sandman72/aZ80_Computer/Software/VDP_Firmware/aZ80_VDP/keyboard.ino

//--------------------------------------------------------------------+
// Keyboard Layouts  (three parameters -> lowercase, shifted, altgr )
//--------------------------------------------------------------------+
#define SCANCODE_F1  0x3a
#define SCANCODE_F2  0x3b
#define SCANCODE_F3  0x3c
#define SCANCODE_F4  0x3d
#define SCANCODE_F5  0x3e
#define SCANCODE_F6  0x3f
#define SCANCODE_F7  0x40
#define SCANCODE_F8  0x41
#define SCANCODE_F9  0x42
#define SCANCODE_F10 0x43
#define SCANCODE_F11 0x44
#define SCANCODE_F12 0x45

#define SCANCODE_HOME   0x4a
#define SCANCODE_PGUP   0x4b
#define SCANCODE_PGDOWN 0x4e
#define SCANCODE_RIGHT  0x4f
#define SCANCODE_LEFT   0x50
#define SCANCODE_DOWN   0x51
#define SCANCODE_UP     0x52

#define HID_KEYCODE_TO_ASCII_US     \
    {0     , 0     ,0 }, /* 0x00 */ \
    {0     , 0     ,0 }, /* 0x01 */ \
    {0     , 0     ,0 }, /* 0x02 */ \
    {0     , 0     ,0 }, /* 0x03 */ \
    {'a'   , 'A'   ,0 }, /* 0x04 */ \
    {'b'   , 'B'   ,0 }, /* 0x05 */ \
    {'c'   , 'C'   ,0 }, /* 0x06 */ \
    {'d'   , 'D'   ,0 }, /* 0x07 */ \
    {'e'   , 'E'   ,0 }, /* 0x08 */ \
    {'f'   , 'F'   ,0 }, /* 0x09 */ \
    {'g'   , 'G'   ,0 }, /* 0x0a */ \
    {'h'   , 'H'   ,0 }, /* 0x0b */ \
    {'i'   , 'I'   ,0 }, /* 0x0c */ \
    {'j'   , 'J'   ,0 }, /* 0x0d */ \
    {'k'   , 'K'   ,0 }, /* 0x0e */ \
    {'l'   , 'L'   ,0 }, /* 0x0f */ \
    {'m'   , 'M'   ,0 }, /* 0x10 */ \
    {'n'   , 'N'   ,0 }, /* 0x11 */ \
    {'o'   , 'O'   ,0 }, /* 0x12 */ \
    {'p'   , 'P'   ,0 }, /* 0x13 */ \
    {'q'   , 'Q'   ,0 }, /* 0x14 */ \
    {'r'   , 'R'   ,0 }, /* 0x15 */ \
    {'s'   , 'S'   ,0 }, /* 0x16 */ \
    {'t'   , 'T'   ,0 }, /* 0x17 */ \
    {'u'   , 'U'   ,0 }, /* 0x18 */ \
    {'v'   , 'V'   ,0 }, /* 0x19 */ \
    {'w'   , 'W'   ,0 }, /* 0x1a */ \
    {'x'   , 'X'   ,0 }, /* 0x1b */ \
    {'y'   , 'Y'   ,0 }, /* 0x1c */ \
    {'z'   , 'Z'   ,0 }, /* 0x1d */ \
    {'1'   , '!'   ,0 }, /* 0x1e */ \
    {'2'   , '@'   ,0 }, /* 0x1f */ \
    {'3'   , '#'   ,0 }, /* 0x20 */ \
    {'4'   , '$'   ,0 }, /* 0x21 */ \
    {'5'   , '%'   ,0 }, /* 0x22 */ \
    {'6'   , '^'   ,0 }, /* 0x23 */ \
    {'7'   , '&'   ,0 }, /* 0x24 */ \
    {'8'   , '*'   ,0 }, /* 0x25 */ \
    {'9'   , '('   ,0 }, /* 0x26 */ \
    {'0'   , ')'   ,0 }, /* 0x27 */ \
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
    {0     , 0     ,0 }, /* 0x49 INS   */ \
    {0     , 0     ,0 }, /* 0x4a       */ \
    {0     , 0     ,0 }, /* 0x4b PGUP  */ \
    {0x7f  , 0     ,0 }, /* 0x4c DEL   */ \
    {0     , 0     ,0 }, /* 0x4d       */ \
    {0     , 0     ,0 }, /* 0x4e PGDN  */ \
    {0     , 0     ,0 }, /* 0x4f RIGHT */ \
    {0     , 0     ,0 }, /* 0x50 LEFT  */ \
    {0     , 0     ,0 }, /* 0x51 DOWN  */ \
    {0     , 0     ,0 }, /* 0x52 UP    */ \
    {0     , 0     ,0 }, /* 0x53       */ \
    {'/'   , '/'   ,0 }, /* 0x54 */ \
    {'*'   , '*'   ,0 }, /* 0x55 */ \
    {'-'   , '-'   ,0 }, /* 0x56 */ \
    {'+'   , '+'   ,0 }, /* 0x57 */ \
    {'\r'  , '\r'  ,0 }, /* 0x58 */ \
    {'1'   , 0     ,0 }, /* 0x59 */ \
    {'2'   , 0     ,0 }, /* 0x5a */ \
    {'3'   , 0     ,0 }, /* 0x5b */ \
    {'4'   , 0     ,0 }, /* 0x5c */ \
    {'5'   , '5'   ,0 }, /* 0x5d */ \
    {'6'   , 0     ,0 }, /* 0x5e */ \
    {'7'   , 0     ,0 }, /* 0x5f */ \
    {'8'   , 0     ,0 }, /* 0x60 */ \
    {'9'   , 0     ,0 }, /* 0x61 */ \
    {'0'   , 0     ,0 }, /* 0x62 */ \
    {'0'   , 0     ,0 }, /* 0x63 */ \
    {'='   , '='   ,0 }, /* 0x67 */ \

#define HID_KEYCODE_TO_ASCII_UK     \
    {0     , 0     ,0 }, /* 0x00 */ \
    {0     , 0     ,0 }, /* 0x01 */ \
    {0     , 0     ,0 }, /* 0x02 */ \
    {0     , 0     ,0 }, /* 0x03 */ \
    {'a'   , 'A'   ,0 }, /* 0x04 */ \
    {'b'   , 'B'   ,0 }, /* 0x05 */ \
    {'c'   , 'C'   ,0 }, /* 0x06 */ \
    {'d'   , 'D'   ,0 }, /* 0x07 */ \
    {'e'   , 'E'   ,0 }, /* 0x08 */ \
    {'f'   , 'F'   ,0 }, /* 0x09 */ \
    {'g'   , 'G'   ,0 }, /* 0x0a */ \
    {'h'   , 'H'   ,0 }, /* 0x0b */ \
    {'i'   , 'I'   ,0 }, /* 0x0c */ \
    {'j'   , 'J'   ,0 }, /* 0x0d */ \
    {'k'   , 'K'   ,0 }, /* 0x0e */ \
    {'l'   , 'L'   ,0 }, /* 0x0f */ \
    {'m'   , 'M'   ,0 }, /* 0x10 */ \
    {'n'   , 'N'   ,0 }, /* 0x11 */ \
    {'o'   , 'O'   ,0 }, /* 0x12 */ \
    {'p'   , 'P'   ,0 }, /* 0x13 */ \
    {'q'   , 'Q'   ,0 }, /* 0x14 */ \
    {'r'   , 'R'   ,0 }, /* 0x15 */ \
    {'s'   , 'S'   ,0 }, /* 0x16 */ \
    {'t'   , 'T'   ,0 }, /* 0x17 */ \
    {'u'   , 'U'   ,0 }, /* 0x18 */ \
    {'v'   , 'V'   ,0 }, /* 0x19 */ \
    {'w'   , 'W'   ,0 }, /* 0x1a */ \
    {'x'   , 'X'   ,0 }, /* 0x1b */ \
    {'y'   , 'Y'   ,0 }, /* 0x1c */ \
    {'z'   , 'Z'   ,0 }, /* 0x1d */ \
    {'1'   , '!'   ,0 }, /* 0x1e */ \
    {'2'   , '\"'  ,0 }, /* 0x1f */ \
    {'3'   , '#'   ,0 }, /* 0x20 */ \
    {'4'   , '$'   ,0 }, /* 0x21 */ \
    {'5'   , '%'   ,0 }, /* 0x22 */ \
    {'6'   , '^'   ,0 }, /* 0x23 */ \
    {'7'   , '&'   ,0 }, /* 0x24 */ \
    {'8'   , '*'   ,0 }, /* 0x25 */ \
    {'9'   , '('   ,0 }, /* 0x26 */ \
    {'0'   , ')'   ,0 }, /* 0x27 */ \
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
    {0     , 0     ,0 }, /* 0x49 INS   */ \
    {0     , 0     ,0 }, /* 0x4a       */ \
    {0     , 0     ,0 }, /* 0x4b PGUP  */ \
    {0     , 0     ,0 }, /* 0x4c DEL   */ \
    {0     , 0     ,0 }, /* 0x4d       */ \
    {0     , 0     ,0 }, /* 0x4e PGDN  */ \
    {0     , 0     ,0 }, /* 0x4f RIGHT */ \
    {0     , 0     ,0 }, /* 0x50 LEFT  */ \
    {0     , 0     ,0 }, /* 0x51 DOWN  */ \
    {0     , 0     ,0 }, /* 0x52 UP    */ \
    {0     , 0     ,0 }, /* 0x53       */ \
    {'/'   , '/'   ,0 }, /* 0x54 */ \
    {'*'   , '*'   ,0 }, /* 0x55 */ \
    {'-'   , '-'   ,0 }, /* 0x56 */ \
    {'+'   , '+'   ,0 }, /* 0x57 */ \
    {'\r'  , '\r'  ,0 }, /* 0x58 */ \
    {'1'   , 0     ,0 }, /* 0x59 */ \
    {'2'   , 0     ,0 }, /* 0x5a */ \
    {'3'   , 0     ,0 }, /* 0x5b */ \
    {'4'   , 0     ,0 }, /* 0x5c */ \
    {'5'   , '5'   ,0 }, /* 0x5d */ \
    {'6'   , 0     ,0 }, /* 0x5e */ \
    {'7'   , 0     ,0 }, /* 0x5f */ \
    {'8'   , 0     ,0 }, /* 0x60 */ \
    {'9'   , 0     ,0 }, /* 0x61 */ \
    {'0'   , 0     ,0 }, /* 0x62 */ \
    {'0'   , 0     ,0 }, /* 0x63 */ \
    {'\\'  , '|'   ,0 }, /* 0x64 */ \
    {'0'   , 0     ,0 }, /* 0x65 */ \
    {'0'   , 0     ,0 }, /* 0x66 */ \
    {'='   , '='   ,0 }, /* 0x67 */ \

#define HID_KEYCODE_TO_ASCII_DE      \
     {0     , 0     ,0 }, /* 0x00 */ \
     {0     , 0     ,0 }, /* 0x01 */ \
     {0     , 0     ,0 }, /* 0x02 */ \
     {0     , 0     ,0 }, /* 0x03 */ \
     {'a'   , 'A'   ,0 }, /* 0x04 */ \
     {'b'   , 'B'   ,0 }, /* 0x05 */ \
     {'c'   , 'C'   ,0 }, /* 0x06 */ \
     {'d'   , 'D'   ,0 }, /* 0x07 */ \
     {'e'   , 'E'   ,0 }, /* 0x08 */ \
     {'f'   , 'F'   ,0 }, /* 0x09 */ \
     {'g'   , 'G'   ,0 }, /* 0x0a */ \
     {'h'   , 'H'   ,0 }, /* 0x0b */ \
     {'i'   , 'I'   ,0 }, /* 0x0c */ \
     {'j'   , 'J'   ,0 }, /* 0x0d */ \
     {'k'   , 'K'   ,0 }, /* 0x0e */ \
     {'l'   , 'L'   ,0 }, /* 0x0f */ \
     {'m'   , 'M'   ,0 }, /* 0x10 */ \
     {'n'   , 'N'   ,0 }, /* 0x11 */ \
     {'o'   , 'O'   ,0 }, /* 0x12 */ \
     {'p'   , 'P'   ,0 }, /* 0x13 */ \
     {'q'   , 'Q' , '@'}, /* 0x14 */ \
     {'r'   , 'R'   ,0 }, /* 0x15 */ \
     {'s'   , 'S'   ,0 }, /* 0x16 */ \
     {'t'   , 'T'   ,0 }, /* 0x17 */ \
     {'u'   , 'U'   ,0 }, /* 0x18 */ \
     {'v'   , 'V'   ,0 }, /* 0x19 */ \
     {'w'   , 'W'   ,0 }, /* 0x1a */ \
     {'x'   , 'X'   ,0 }, /* 0x1b */ \
     {'z'   , 'Z'   ,0 }, /* 0x1c */ \
     {'y'   , 'Y'   ,0 }, /* 0x1d */ \
     {'1'   , '!'   ,0 }, /* 0x1e */ \
     {'2'   , '\"'  ,0 }, /* 0x1f */ \
     {'3'   , 0     ,0 }, /* 0x20 */ \
     {'4'   , '$'   ,0 }, /* 0x21 */ \
     {'5'   , '%'   ,0 }, /* 0x22 */ \
     {'6'   , '&'   ,0 }, /* 0x23 */ \
     {'7'   , '/' ,'{' }, /* 0x24 */ \
     {'8'   , '(' ,'[' }, /* 0x25 */ \
     {'9'   , ')' ,']' }, /* 0x26 */ \
     {'0'   , '=' ,'}' }, /* 0x27 */ \
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
     {0     , 0     ,0 }, /* 0x49 INS   */ \
     {0     , 0     ,0 }, /* 0x4a       */ \
     {0     , 0     ,0 }, /* 0x4b PGUP  */ \
     {0x7f  , 0     ,0 }, /* 0x4c DEL   */ \
     {0     , 0     ,0 }, /* 0x4d       */ \
     {0     , 0     ,0 }, /* 0x4e PGDN  */ \
     {0     , 0     ,0 }, /* 0x4f RIGHT */ \
     {0     , 0     ,0 }, /* 0x50 LEFT  */ \
     {0     , 0     ,0 }, /* 0x51 DOWN  */ \
     {0     , 0     ,0 }, /* 0x52 UP    */ \
     {0     , 0     ,0 }, /* 0x53       */ \
     {'/'   , '/'   ,0 }, /* 0x54 */ \
     {'*'   , '*'   ,0 }, /* 0x55 */ \
     {'-'   , '-'   ,0 }, /* 0x56 */ \
     {'+'   , '+'   ,0 }, /* 0x57 */ \
     {'\r'  , '\r'  ,0 }, /* 0x58 */ \
     {'1'   , 0     ,0 }, /* 0x59 */ \
     {'2'   , 0     ,0 }, /* 0x5a */ \
     {'3'   , 0     ,0 }, /* 0x5b */ \
     {'4'   , 0     ,0 }, /* 0x5c */ \
     {'5'   , '5'   ,0 }, /* 0x5d */ \
     {'6'   , 0     ,0 }, /* 0x5e */ \
     {'7'   , 0     ,0 }, /* 0x5f */ \
     {'8'   , 0     ,0 }, /* 0x60 */ \
     {'9'   , 0     ,0 }, /* 0x61 */ \
     {'0'   , 0     ,0 }, /* 0x62 */ \
     {'.'   , 0     ,0 }, /* 0x63 */ \
     {'<' , '>'   ,'|' }, /* 0x64 */ \
     {'0'   , 0     ,0 }, /* 0x65 */ \
     {'0'   , 0     ,0 }, /* 0x66 */ \
     {'='   , '='   ,0 }, /* 0x67 */ \

#define HID_KEYCODE_TO_ASCII_FR      \
     {0     , 0     ,0 }, /* 0x00 */ \
     {0     , 0     ,0 }, /* 0x01 */ \
     {0     , 0     ,0 }, /* 0x02 */ \
     {0     , 0     ,0 }, /* 0x03 */ \
     {'q'   , 'Q'   ,0 }, /* 0x04 */ \
     {'b'   , 'B'   ,0 }, /* 0x05 */ \
     {'c'   , 'C'   ,0 }, /* 0x06 */ \
     {'d'   , 'D'   ,0 }, /* 0x07 */ \
     {'e'   , 'E'   ,0 }, /* 0x08 (alt=EUR)*/ \
     {'f'   , 'F'   ,0 }, /* 0x09 */ \
     {'g'   , 'G'   ,0 }, /* 0x0a */ \
     {'h'   , 'H'   ,0 }, /* 0x0b */ \
     {'i'   , 'I'   ,0 }, /* 0x0c */ \
     {'j'   , 'J'   ,0 }, /* 0x0d */ \
     {'k'   , 'K'   ,0 }, /* 0x0e */ \
     {'l'   , 'L'   ,0 }, /* 0x0f */ \
     {','   , '?'   ,0 }, /* 0x10 */ \
     {'n'   , 'N'   ,0 }, /* 0x11 */ \
     {'o'   , 'O'   ,0 }, /* 0x12 */ \
     {'p'   , 'P'   ,0 }, /* 0x13 */ \
     {'a'   , 'A'  ,'@'}, /* 0x14 */ \
     {'r'   , 'R'   ,0 }, /* 0x15 */ \
     {'s'   , 'S'   ,0 }, /* 0x16 */ \
     {'t'   , 'T'   ,0 }, /* 0x17 */ \
     {'u'   , 'U'   ,0 }, /* 0x18 */ \
     {'v'   , 'V'   ,0 }, /* 0x19 */ \
     {'z'   , 'Z'   ,0 }, /* 0x1a */ \
     {'x'   , 'X'   ,0 }, /* 0x1b */ \
     {'y'   , 'Y'   ,0 }, /* 0x1c */ \
     {'w'   , 'W'   ,0 }, /* 0x1d */ \
     {'&'   , '1'   ,0 }, /* 0x1e */ \
     {'e'   , '2'  ,'~'}, /* 0x1f =é */ \
     {'\"'  , '3'  ,'#'}, /* 0x20 */ \
     {'\''  , '4'  ,'{'}, /* 0x21 */ \
     {'('   , '5'  ,'['}, /* 0x22 */ \
     {'-'   , '6'  ,'|'}, /* 0x23 */ \
     {'e'   , '7'  ,'`'}, /* 0x24 =è */ \
     {'_'   , '8' ,'\\'}, /* 0x25 */ \
     {'c'   , '9'  ,'^'}, /* 0x26 =ç */ \
     {'a'   , '0'  ,'@'}, /* 0x27 =à */ \
     {'\r'  , '\r'  ,0 }, /* 0x28 */ \
     {'\x1b', '\x1b',0 }, /* 0x29 */ \
     {'\b'  , '\b'  ,0 }, /* 0x2a */ \
     {'\t'  , '\t'  ,0 }, /* 0x2b */ \
     {' '   , ' '   ,0 }, /* 0x2c */ \
     {')'   , 0    ,']'}, /* 0x2d shift=° */ \
     {'='   , '+'  ,'}'}, /* 0x2e */ \
     {'^'   , 0     ,0 }, /* 0x2f shift=tréma(named Diaeresis in english) */ \
     {'$'   , '&'   ,0 }, /* 0x30 alt=crossed_circle*/ \
     {'#'   , '\''  ,0 }, /* 0x31 */ \
     {'*'   , 'u'   ,0 }, /* 0x32 (on right of $34, shift=µ)*/ \
     {'m'   , 'M'   ,0 }, /* 0x33 */ \
     {'u'   , '%'   ,0 }, /* 0x34 ù */ \
     {'`'   , '~'   ,0 }, /* 0x35 (not correct but changed!)*/ \
     {';'   , '.'   ,0 }, /* 0x36 */ \
     {':'   , '/'   ,0 }, /* 0x37 */ \
     {'!'   , '!'   ,0 }, /* 0x38 shift=§*/ \
     {0     , 0     ,0 }, /* 0x39 */ \
     {'['   , 0     ,0 }, /* 0x3a F1 */ \
     {']'   , 0     ,0 }, /* 0x3b F2 */ \
     {'{'   , 0     ,0 }, /* 0x3c F3 */ \
     {'}'   , 0     ,0 }, /* 0x3d F4 */ \
     {'|'   , 0     ,0 }, /* 0x3e F5 */ \
     {'@'   , 0     ,0 }, /* 0x3f F6 */ \
     {'\\'  , 0     ,0 }, /* 0x40 F7 */ \
     {'#'   , 0     ,0 }, /* 0x41 F8 */ \
     {0     , 0     ,0 }, /* 0x42 F9 */ \
     {0     , 0     ,0 }, /* 0x43 F10 */ \
     {0     , 0     ,0 }, /* 0x44 F11 */ \
     {0     , 0     ,0 }, /* 0x45 F12 */ \
     {0     , 0     ,0 }, /* 0x46 Print Screen*/ \
     {0     , 0     ,0 }, /* 0x47 Scroll Lock */ \
     {0     , 0     ,0 }, /* 0x48 Pause */ \
     {0     , 0     ,0 }, /* 0x49 INS   */ \
     {0     , 0     ,0 }, /* 0x4a       */ \
     {0     , 0     ,0 }, /* 0x4b PGUP  */ \
     {0x7f  , 0     ,0 }, /* 0x4c DEL   */ \
     {0     , 0     ,0 }, /* 0x4d       */ \
     {0     , 0     ,0 }, /* 0x4e PGDN  */ \
     {0     , 0     ,0 }, /* 0x4f RIGHT */ \
     {0     , 0     ,0 }, /* 0x50 LEFT  */ \
     {0     , 0     ,0 }, /* 0x51 DOWN  */ \
     {0     , 0     ,0 }, /* 0x52 UP    */ \
     {0     , 0     ,0 }, /* 0x53       */ \
     {'/'   , '/'   ,0 }, /* 0x54 */ \
     {'*'   , '*'   ,0 }, /* 0x55 */ \
     {'-'   , '-'   ,0 }, /* 0x56 */ \
     {'+'   , '+'   ,0 }, /* 0x57 */ \
     {'\r'  , '\r'  ,0 }, /* 0x58 */ \
     {'1'   , 0     ,0 }, /* 0x59 */ \
     {'2'   , 0     ,0 }, /* 0x5a */ \
     {'3'   , 0     ,0 }, /* 0x5b */ \
     {'4'   , 0     ,0 }, /* 0x5c */ \
     {'5'   , '5'   ,0 }, /* 0x5d */ \
     {'6'   , 0     ,0 }, /* 0x5e */ \
     {'7'   , 0     ,0 }, /* 0x5f */ \
     {'8'   , 0     ,0 }, /* 0x60 */ \
     {'9'   , 0     ,0 }, /* 0x61 */ \
     {'0'   , 0     ,0 }, /* 0x62 */ \
     {'.'   , 0     ,0 }, /* 0x63 */ \
     {'<'  , '>'  ,'|' }, /* 0x64 */ \
     {'0'   , 0     ,0 }, /* 0x65 Menu */ \
     {'0'   , 0     ,0 }, /* 0x66 */ \
     {'='   , '='   ,0 }, /* 0x67 */ \
